Lexy1972/Reverse-Engineer-a-Quntis-Monitor-LED-Bar-Controller/Images/Logic Analyzer cmd 0x25.png

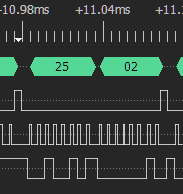
Images/Logic Analyzer cmd 0x25.png
